norbertg1/WateringSystem_client-HW/pics/IMG_20180405_111201.jpg

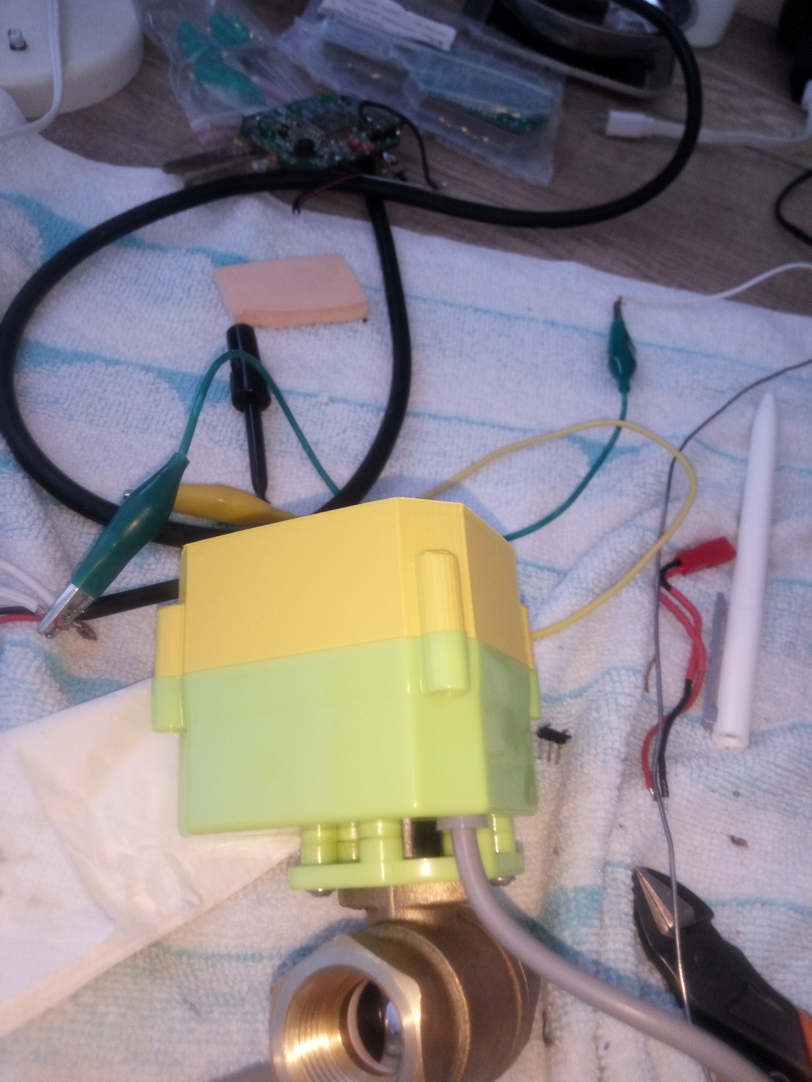
pics/IMG_20180405_111201.jpg
