norbertg1/WateringSystem_client-HW/pics/IMG_20180410_012313.jpg

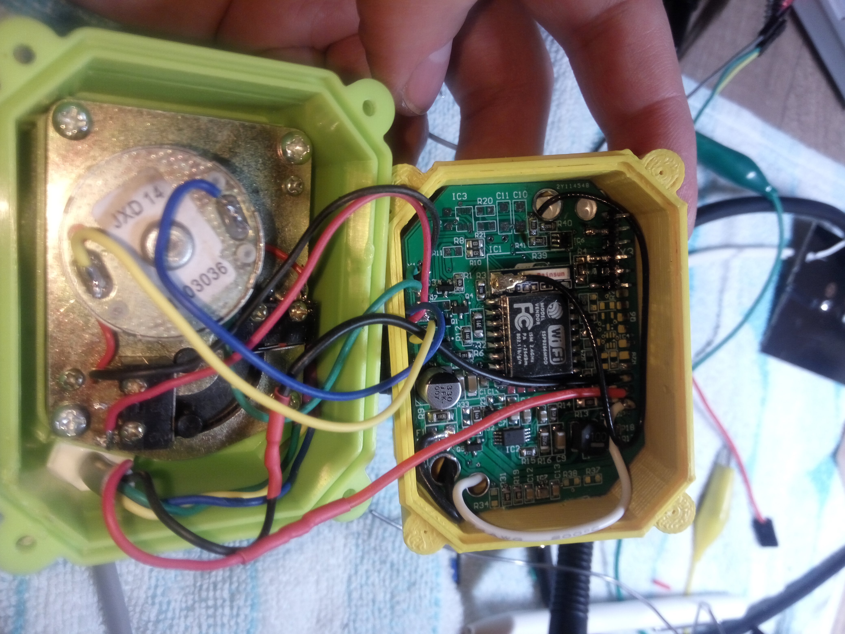
pics/IMG_20180410_012313.jpg
