norbertg1/WateringSystem_client-HW/pics/IMG_20180706_124230.jpg

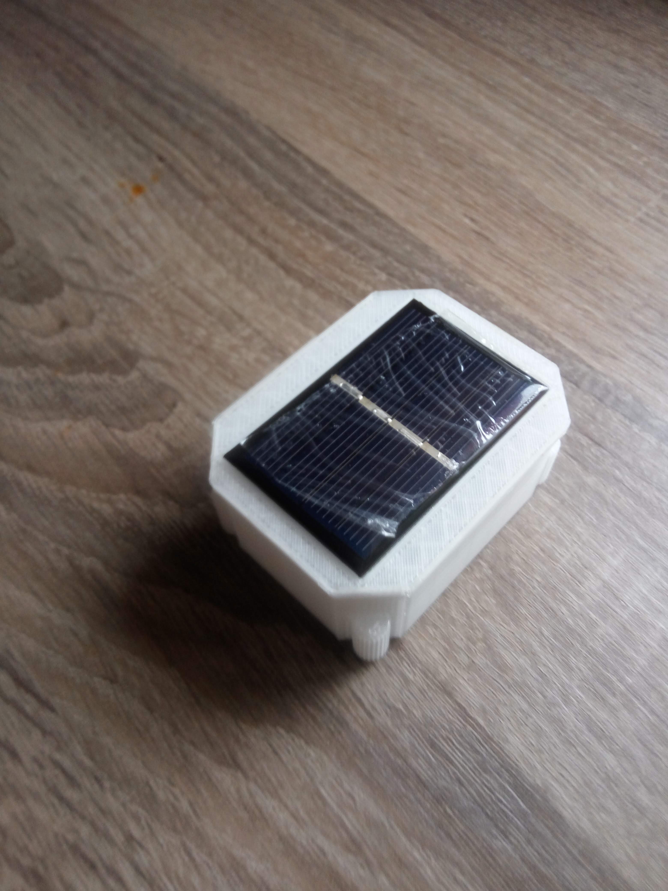
pics/IMG_20180706_124230.jpg
