norbertg1/WateringSystem_client-HW/Soil Moisture sensor simulation.asc

ADCinput: res; 500k
C1: cap; 1000p
C2: cap; 1µ
D1: diode; 1N4148
R1: res; 100k
R2: res; 1000K
V1: voltage; PULSE(0 3 100u 1u 1u 50u 100u)
Named nets: 0
This is the soil electrode
The PWM going from microcontroller
.tran 0 1000m 995m
